mavory/ESP32-home-light-show/Circuit diagram/ESP32.kicad_sch

## KiCad design Circuit diagram/ESP32.kicad_sch (2026-01-05)

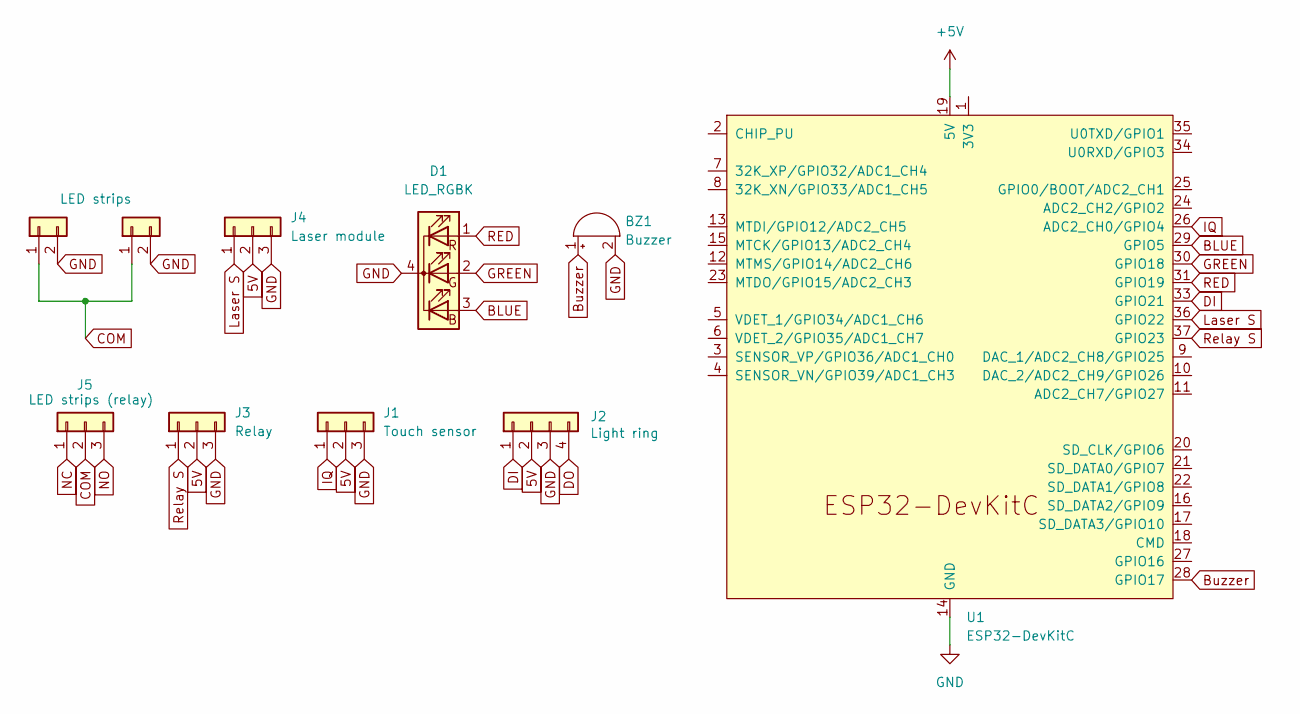
[picture p11: schematic ESP32.kicad_sch]

Parts:
BZ1: Buzzer
D1: LED_RGBK
J1: Touch sensor
J2: Light ring
J3: Relay
J4: Laser module
J5: LED strips (relay)
J6: LED strips
J7: Conn_01x02
U1: ESP32-DevKitC

Connections:
5V: J1.2, J2.2, J3.2, J4.2
+5V: U1.19 (5V)
BLUE: D1.3 (BA), U1.29 (GPIO5)
Buzzer: BZ1.1 (+), U1.28 (GPIO17)
COM: J5.2, J6.1, J7.1
DI: J2.1, U1.33 (GPIO21)
DO: J2.4
GND: BZ1.2 (-), D1.4 (K), J1.3, J2.3, J3.3, J4.3, J6.2, J7.2, U1.14 (GND), U1.32 (GND), U1.38 (GND)
GREEN: D1.2 (GA), U1.30 (GPIO18)
IQ: J1.1, U1.26 (ADC2_CH0/GPIO4)
Laser S: J4.1, U1.36 (GPIO22)
NC: J5.1
NO: J5.3
RED: D1.1 (RA), U1.31 (GPIO19)
Relay S: J3.1, U1.37 (GPIO23)
