mavory/ESP32-home-light-show/Photos/20260104_175004.jpg

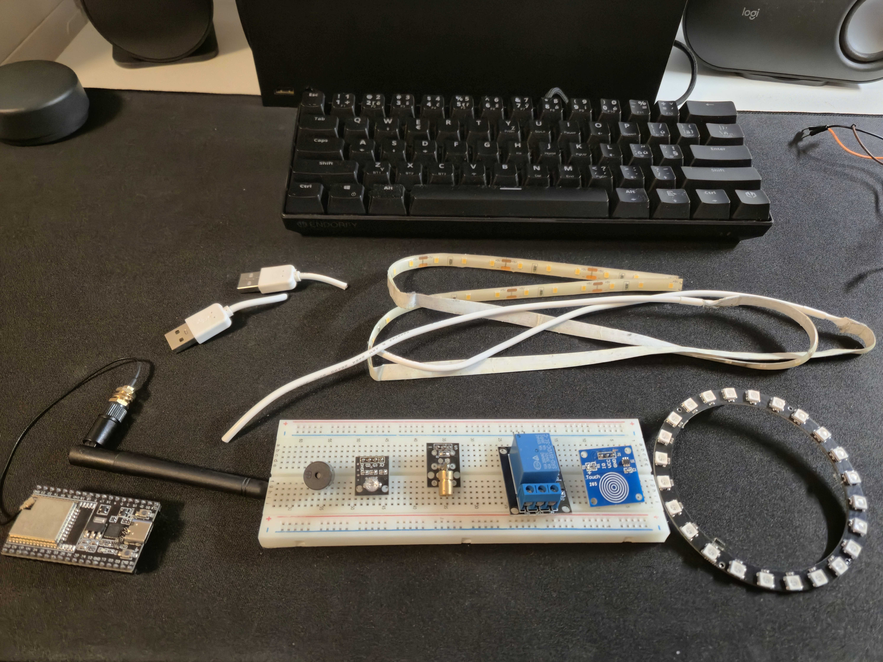
Photos/20260104_175004.jpg
