mavory/ESP32-home-light-show/Photos/20260104_184013.jpg

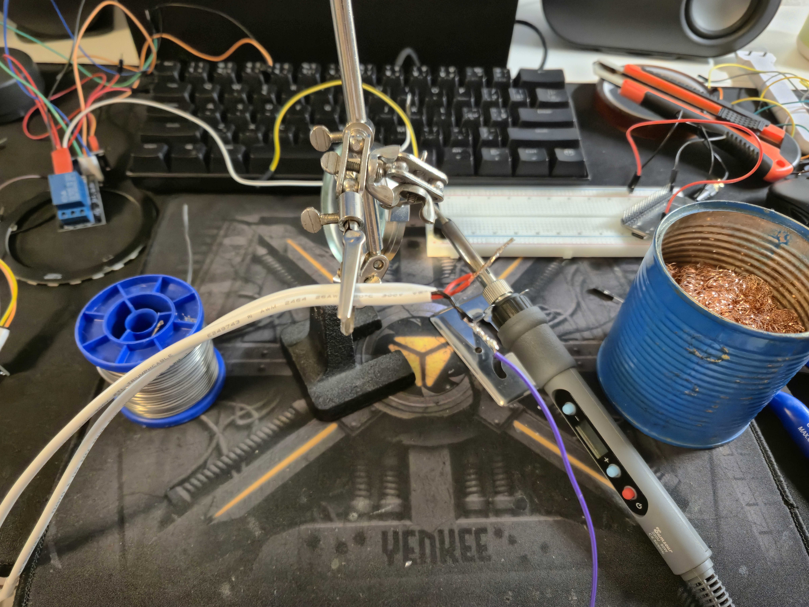
Photos/20260104_184013.jpg
