mavory/ESP32-home-light-show/Photos/20260104_185737.jpg

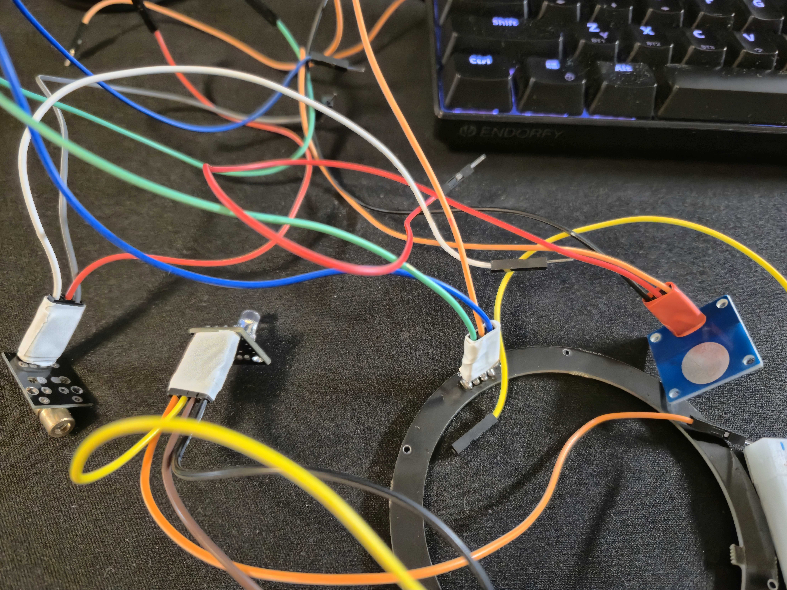
Photos/20260104_185737.jpg
