mavory/ESP32-home-light-show/Photos/20260104_192444.jpg

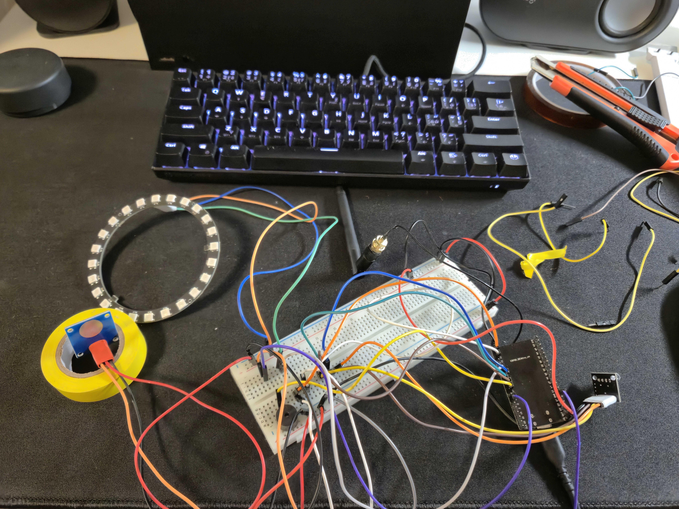
Photos/20260104_192444.jpg
