mavory/ESP32-home-light-show/Photos/20260105_180834.jpg

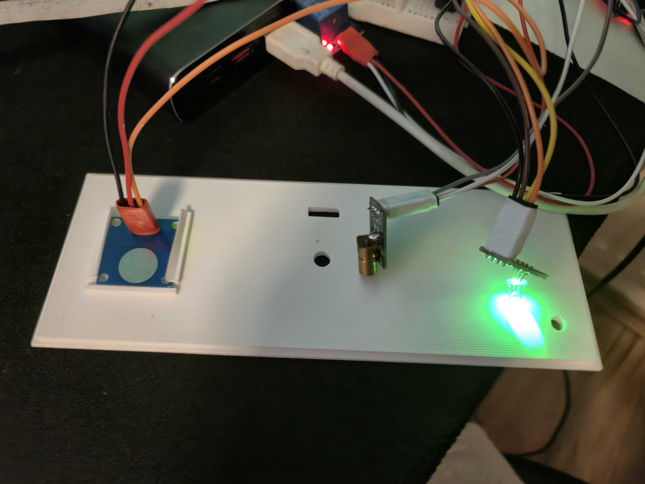
Photos/20260105_180834.jpg
